Arwinplayz/Split-Keyboard-V2/images/Screenshot 2026-01-10 005149.png

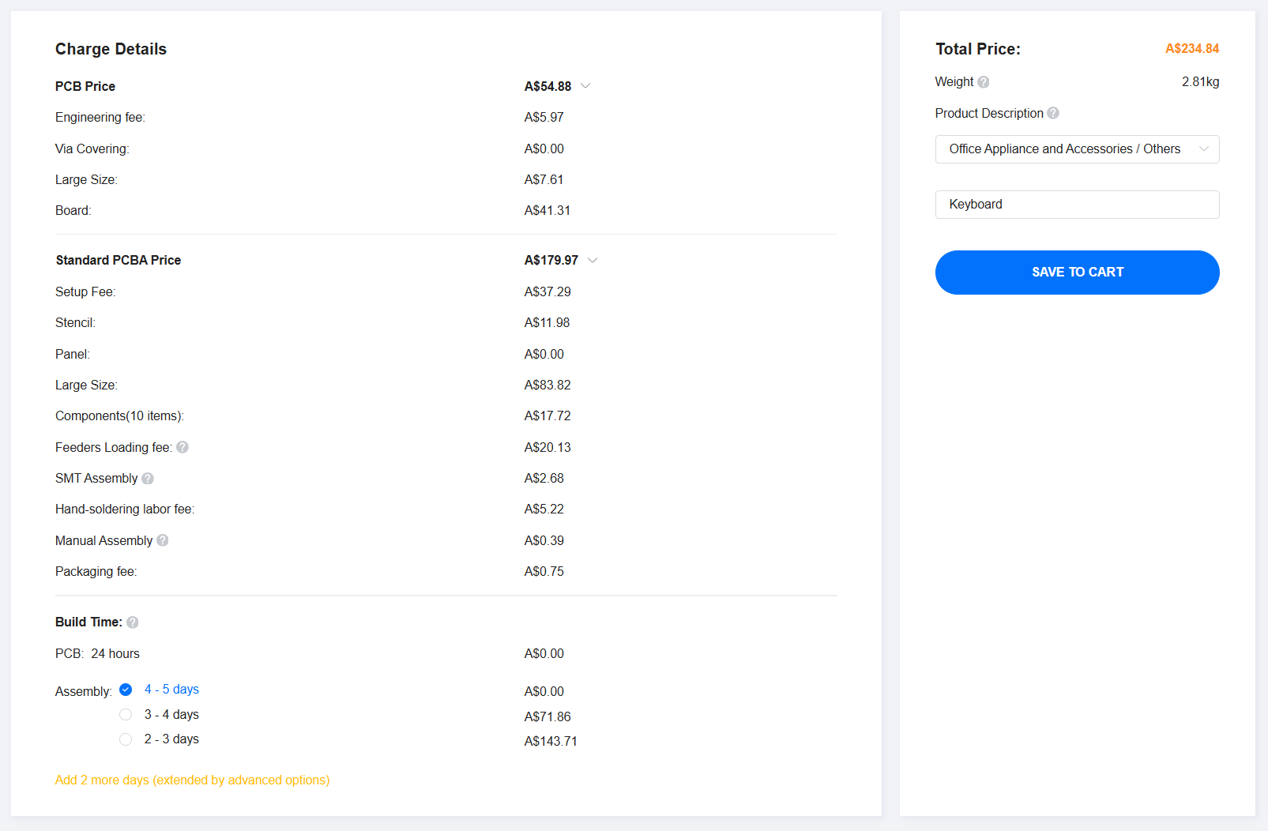
images/Screenshot 2026-01-10 005149.png
